peterheinrich/DA20-C1-ProcedureTrainer/assets/IMG_2492.jpeg

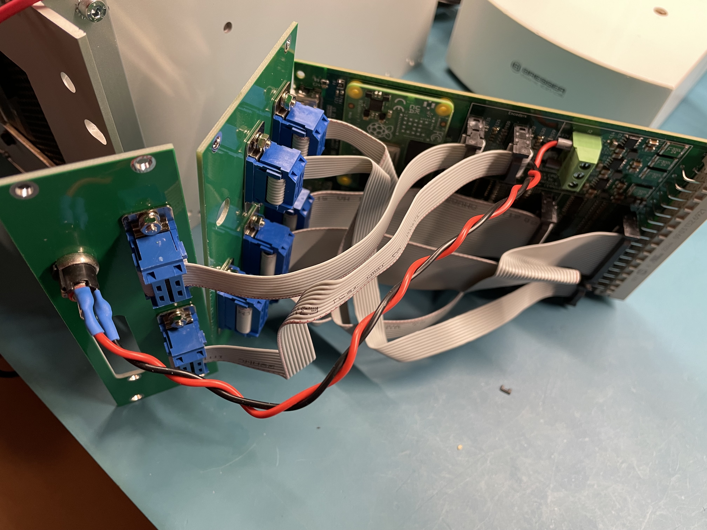
assets/IMG_2492.jpeg
