peterheinrich/DA20-C1-ProcedureTrainer/assets/IMG_2493.jpeg

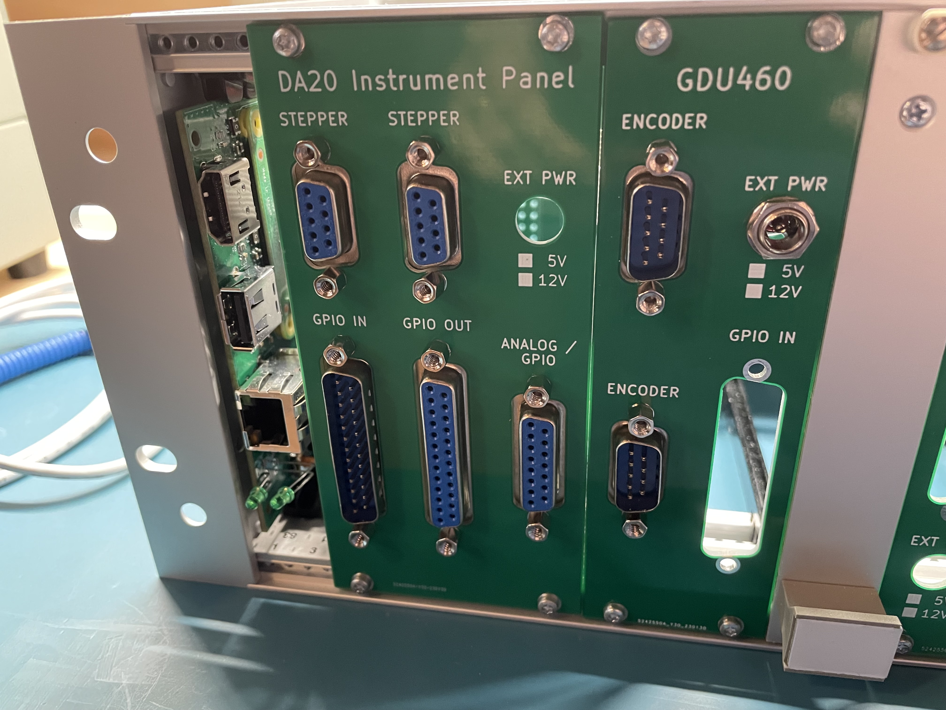
assets/IMG_2493.jpeg
