peterheinrich/DA20-C1-ProcedureTrainer/assets/IMG_2666.jpeg

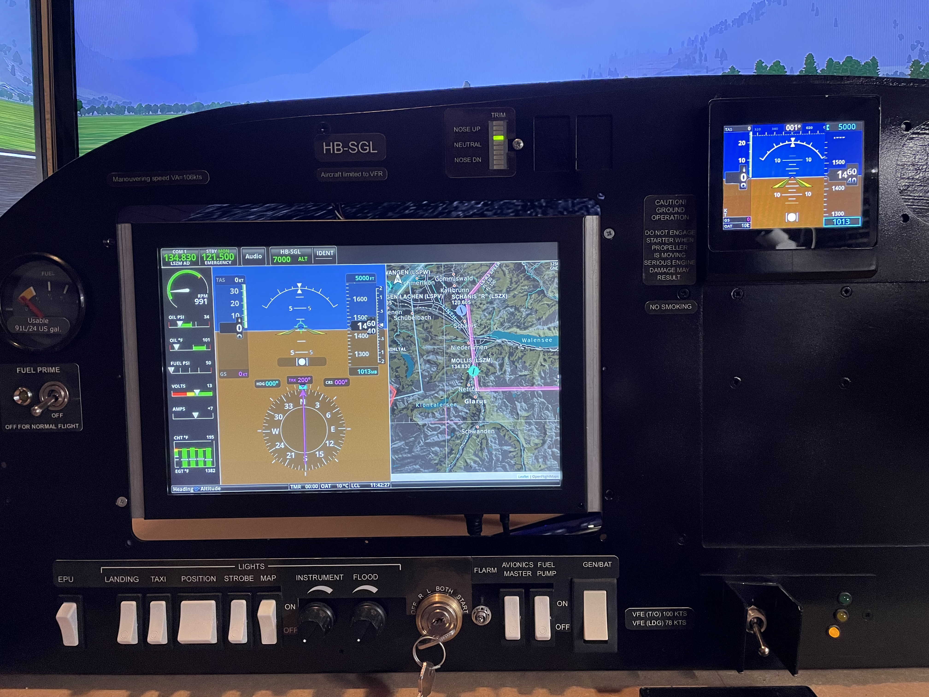
assets/IMG_2666.jpeg
